TjGer22/Hydrom/docs/assets/images/Folie2 (1).png

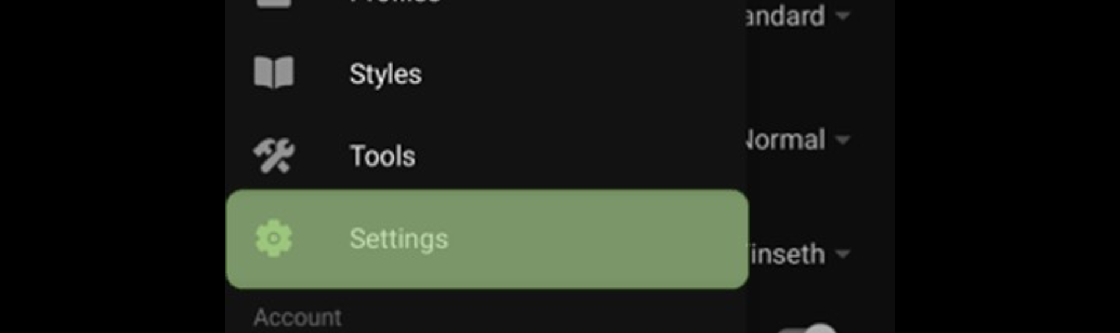
docs/assets/images/Folie2 (1).png
