TjGer22/Hydrom/docs/assets/images/Folie3 (1).png

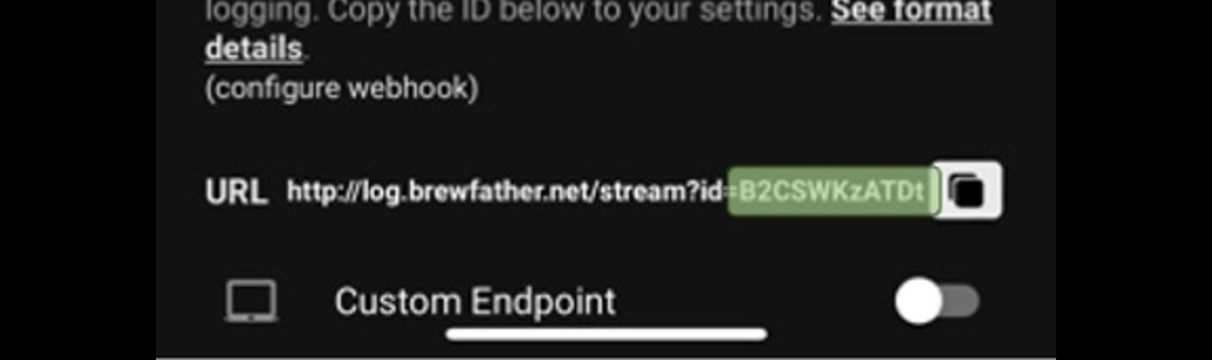
docs/assets/images/Folie3 (1).png
