TjGer22/Hydrom/docs/assets/images/Folie49.png

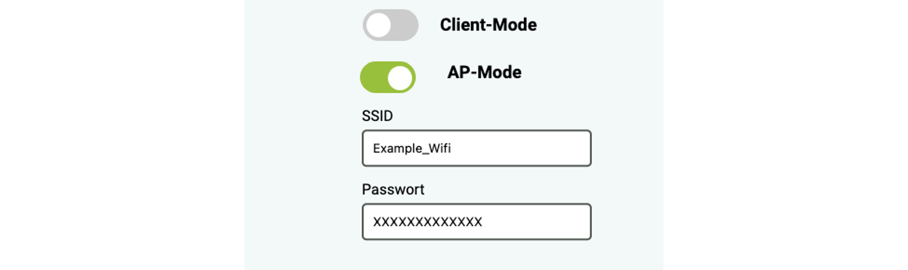
docs/assets/images/Folie49.png
