TjGer22/Hydrom/docs/assets/images/Folie53 (1).png

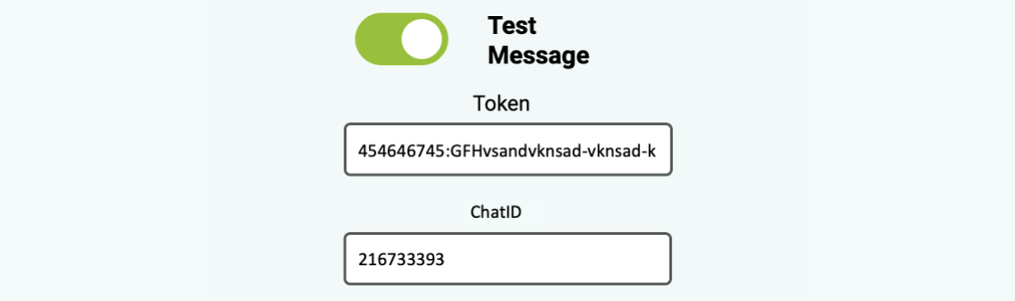
docs/assets/images/Folie53 (1).png
