TjGer22/Hydrom/docs/assets/images/Folie74 (1).png

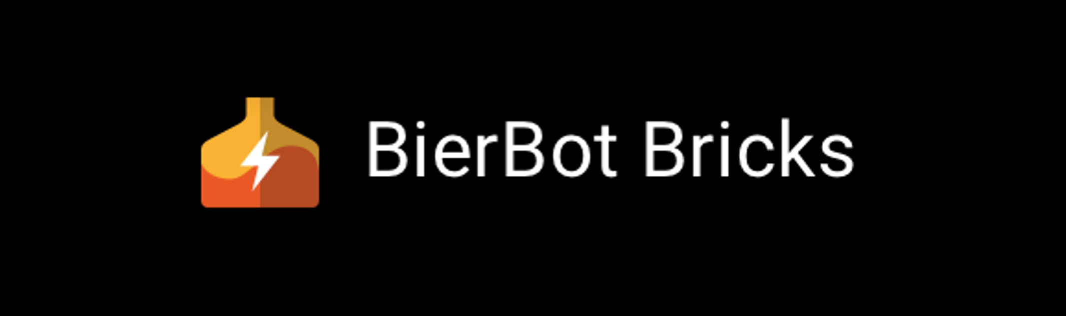
docs/assets/images/Folie74 (1).png
