TjGer22/Hydrom/docs/assets/images/Folie74.png

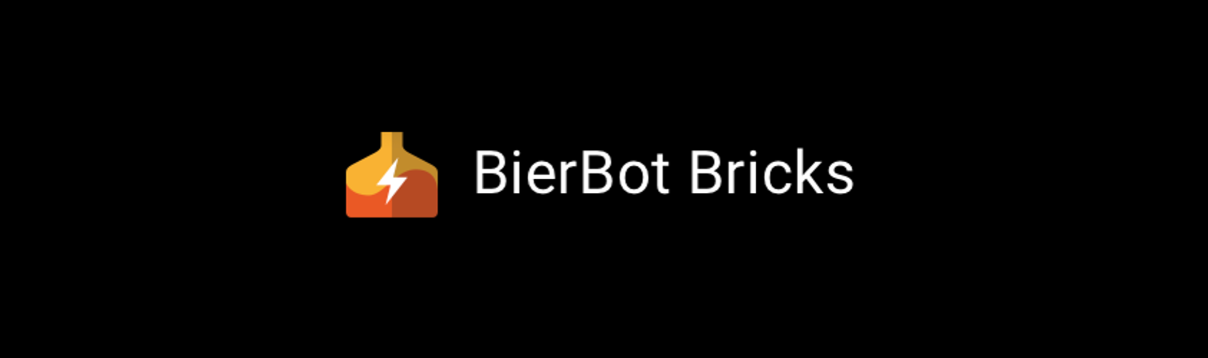
docs/assets/images/Folie74.png
