TjGer22/Hydrom/docs/assets/images/Folie75.png

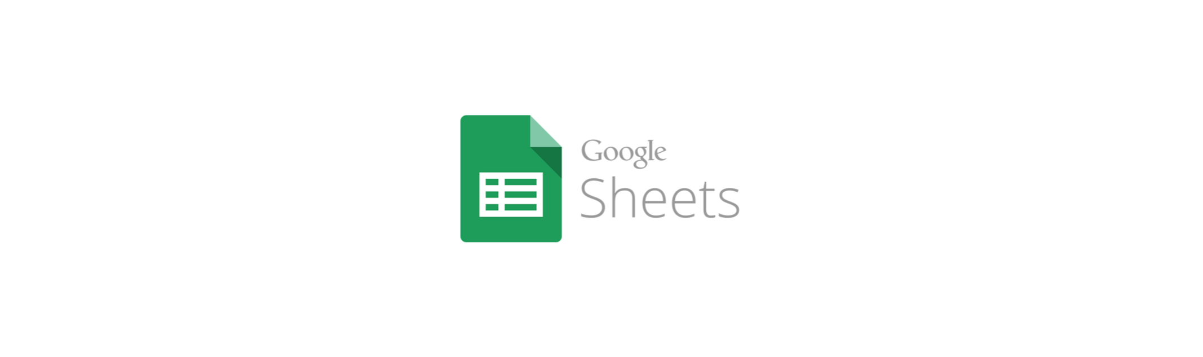
docs/assets/images/Folie75.png
